RBSC/SFG_Cartridge/Case/SFG_Label_v1-Cut.png

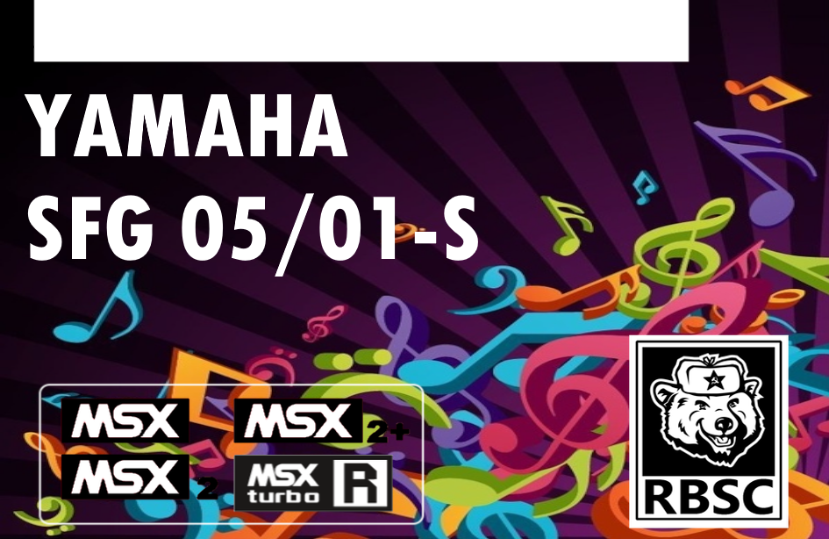
Case/SFG_Label_v1-Cut.png
