RBSC/SFG_Cartridge/Case/SFG_Label_v1-Full.png

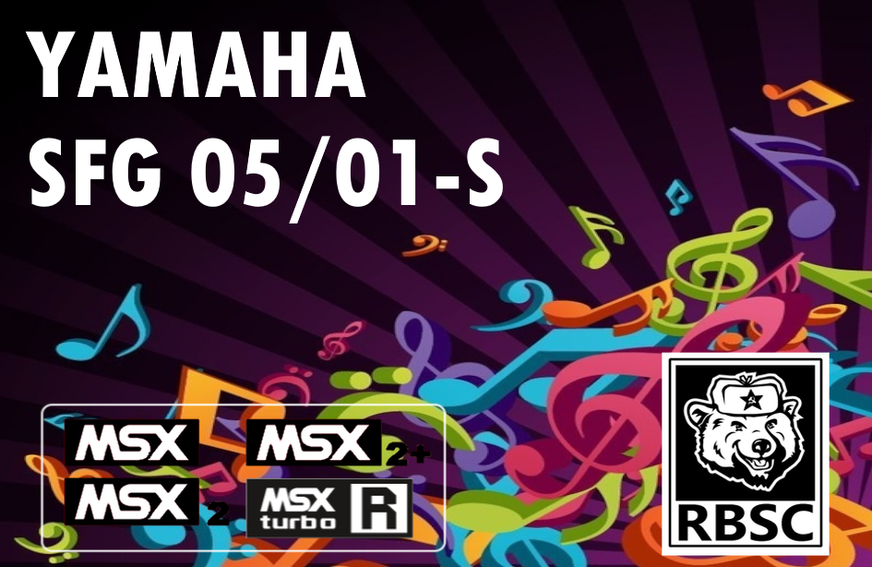
Case/SFG_Label_v1-Full.png
