RBSC/SFG_Cartridge/ExtensionBoard/Pics/exp_board.jpg

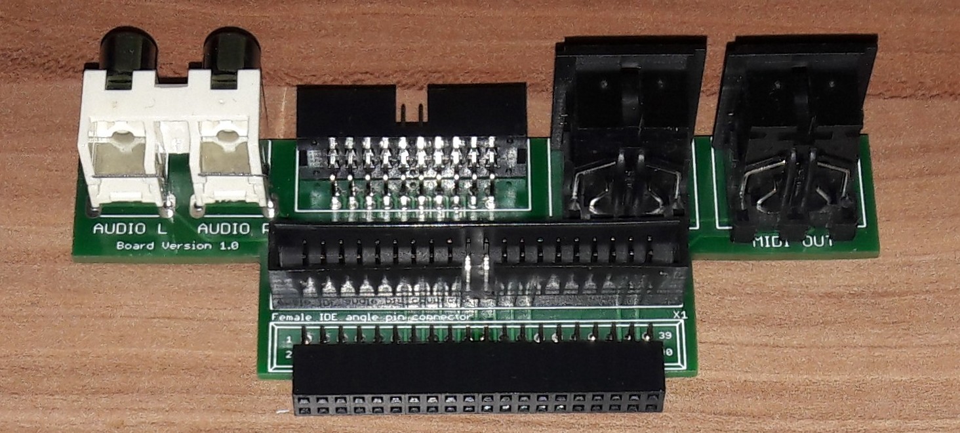
ExtensionBoard/Pics/exp_board.jpg
