RBSC/SFG_Cartridge/Pics/board.jpg

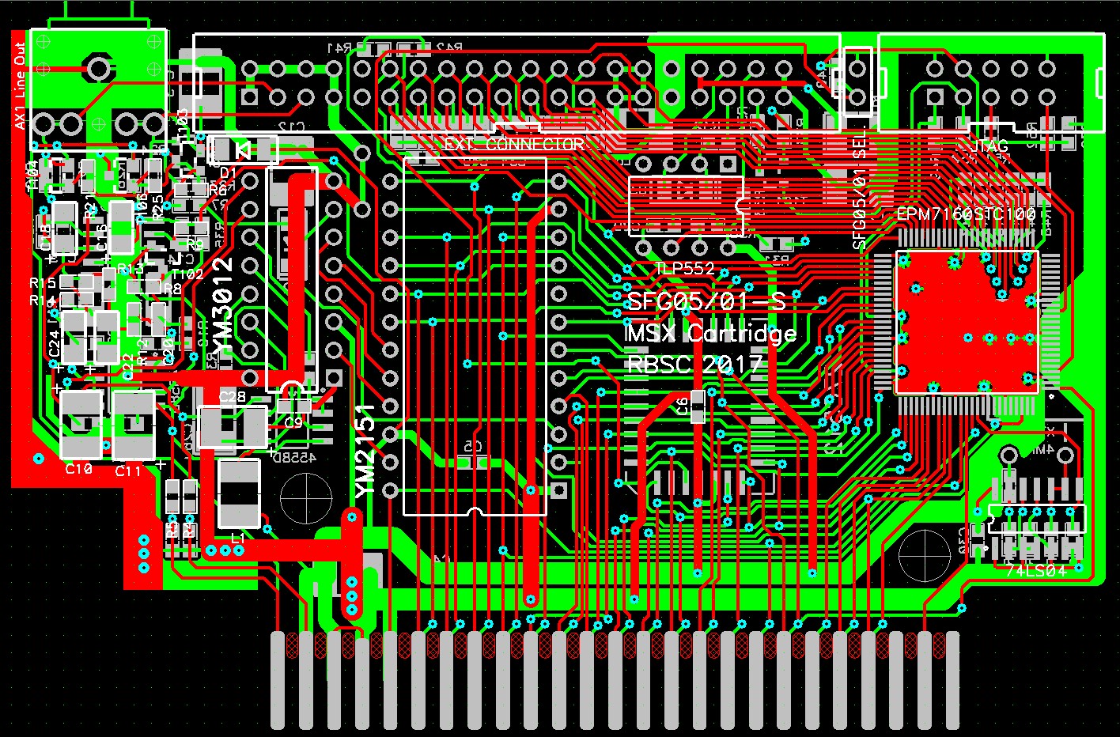
Pics/board.jpg
