RBSC/SFG_Cartridge/Pics/connector.jpg

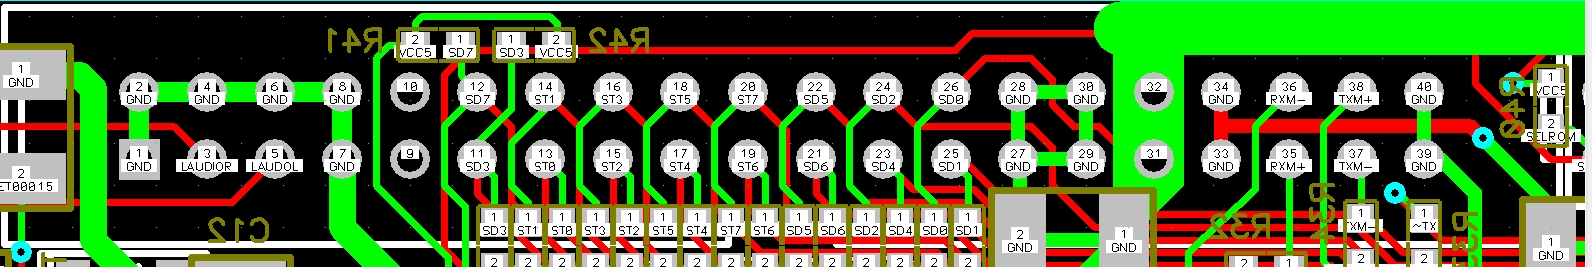
Pics/connector.jpg
