RBSC/SFG_Cartridge/Pics/sfg_v11_front.jpg

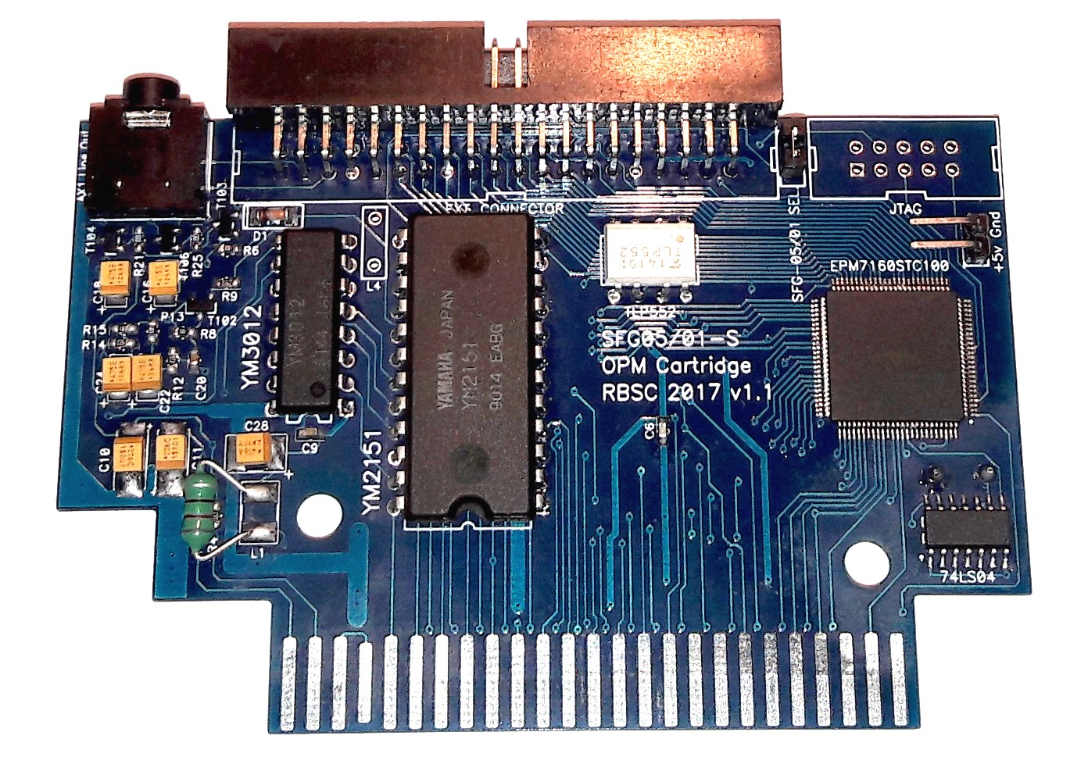
Pics/sfg_v11_front.jpg
