RBSC/SFG_Cartridge/Pics/sfg_v12_front.jpg

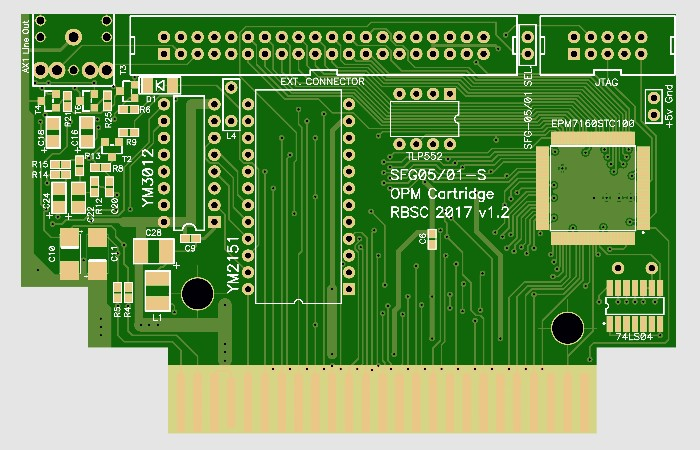
Pics/sfg_v12_front.jpg
