RBSC/SFG_Cartridge/Pics/assembled_cart.jpg

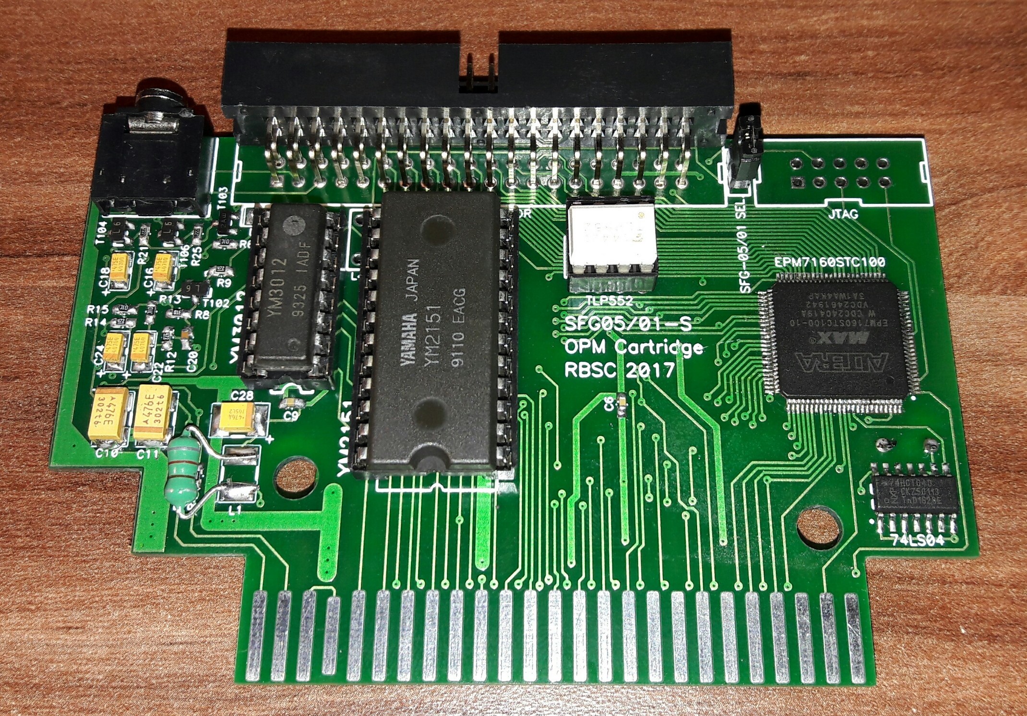
Pics/assembled_cart.jpg
